jelacicedin/AVMS-sensor/Representation/app_screenshot_test.png

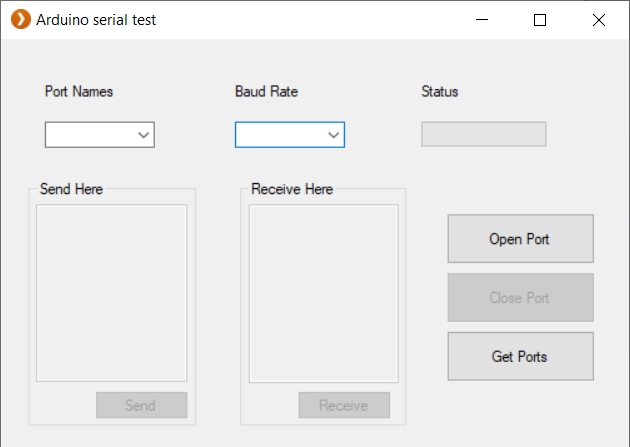
Representation/app_screenshot_test.png
